Michalek007/ESC/ESC Pilot/Pomiary/test2_oscylacje.csv

Time |  |  | Oscillation (%) (avg) | Oscillation (%) (ref)
1749585122.7847323 | 45818.82781 | 0 | 900 | 3
1749585124.4796014 | 45818.82783 | 1.694869855 | 920.75 | 43.61
1749585125.9988434 | 45818.82785 | 3.214110131 | 663.98 | 79.34
1749585127.981447 | 45818.82787 | 5.196709768 | 509.51 | 84.6
1749585129.6124997 | 45818.82789 | 6.827759813 | 350.29 | 78.73
1749585131.2120302 | 45818.82791 | 8.427299769 | 268.96 | 74.82
1749585132.6668863 | 45818.82792 | 9.882150055 | 257.18 | 71.93
1749585134.2183836 | 45818.82794 | 11.43364976 | 210.25 | 67.7
1749585135.769585 | 45818.82796 | 12.98485023 | 179.14 | 64.11
1749585137.2725961 | 45818.82798 | 14.48785958 | 185.46 | 63.46
1749585138.7280366 | 45818.82799 | 15.94329954 | 168.78 | 63.39
1749585140.230938 | 45818.82801 | 17.44620013 | 149.09 | 60.42
1749585141.6537375 | 45818.82803 | 18.8689997 | 133.87 | 57.78
1749585143.0447867 | 45818.82804 | 20.26004966 | 141.51 | 57.1
1749585144.4378734 | 45818.82806 | 21.65313957 | 135.5 | 58.1
1749585145.8917708 | 45818.82808 | 23.10703935 | 123.63 | 55.82
1749585147.2827814 | 45818.82809 | 24.49804971 | 114.04 | 53.8
1749585148.8178267 | 45818.82811 | 26.03308966 | 106.03 | 51.97
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
