Michalek007/ESC/ESC Pilot/Pomiary/test3.csv

Time |  | Time | DutyCycle | ReferenceSpeed | AverageSpeed | MotorState | ró?nica
1749585731.840147 | 45818.83486 | 0 | 105 | 6000 | 6024 | RUN | 24 | Warto?? ?rednia zmierzona | 5999.493976
1749585732.942915 | 45818.83487 | 1.10277012 | 104 | 6000 | 6024 | RUN | 24 | Odchylenie od warto?ci zadanej | 0.506024096
1749585734.0938084 | 45818.83489 | 2.253660327 | 102 | 6000 | 5940 | RUN | -60 | Odchylenie od warto?ci zadanej [%] | 0.008434446
1749585735 | 45818.8349 | 3.389160102 | 105 | 6000 | 6084 | RUN | 84 | maksymalna odchy?ka | 270
1749585736.3650918 | 45818.83491 | 4.524949682 | 103 | 6000 | 5976 | RUN | -24 | odchylenie standardowe | 115.2588886
1749585737.5006552 | 45818.83492 | 5.660509807 | 102 | 6000 | 5928 | RUN | -72 | odchylenie standardowe [%] | 1.920981477
1749585868 | 45818.83643 | 136.1424697 | 105 | 6000 | 5964 | RUN | -36
1749585869 | 45818.83645 | 137.1655694 | 110 | 6000 | 6270 | RUN | 270
1749585870 | 45818.83646 | 0 | 107 | 6000 | 6162 | RUN | 162
1749585871 | 45818.83647 | 1.054739929 | 106 | 6000 | 6090 | RUN | 90
1749585872 | 45818.83649 | 2.093930379 | 102 | 6000 | 5934 | RUN | -66
1749585873 | 45818.8365 | 3.134009731 | 100 | 6000 | 5832 | RUN | -168
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
