Michalek007/ESC/ESC Pilot/Pomiary/test4.csv

Time | DutyCycle | ReferenceSpeed | AverageSpeed | MotorState
1749585855.6062152 | 801 | 4500 | 0 | IDLE
1749585857.748773 | 801 | 4500 | 0 | IDLE
1749585858.7722487 | 801 | 4500 | 0 | IDLE
1749585859.7950497 | 801 | 4500 | 0 | IDLE
1749585860.802953 | 801 | 4500 | 0 | IDLE
1749585861.7937887 | 801 | 4500 | 0 | IDLE
1749585862.8499117 | 801 | 4500 | 0 | IDLE
1749585863.9212673 | 233 | 4500 | 492 | START
1749585864.9446652 | 108 | 6000 | 3216 | RUN
1749585865.9522288 | 105 | 6000 | 5190 | RUN
1749585866.975492 | 102 | 6000 | 5664 | RUN
1749585867.9826145 | 105 | 6000 | 5964 | RUN
1749585869.00571 | 110 | 6000 | 6270 | RUN
1749585870.2697713 | 107 | 6000 | 6162 | RUN
1749585871.3245144 | 106 | 6000 | 6090 | RUN
1749585872.3637047 | 102 | 6000 | 5934 | RUN
1749585873.4037893 | 100 | 6000 | 5832 | RUN
1749585874.4749014 | 102 | 6000 | 5922 | RUN
1749585875.514549 | 100 | 6000 | 5862 | RUN
1749585876.5856402 | 102 | 6000 | 5934 | RUN
1749585877.5934482 | 104 | 6000 | 6006 | RUN
1749585878.5848978 | 105 | 6000 | 6054 | RUN
1749585879.5759685 | 104 | 6000 | 6036 | RUN
1749585880.583357 | 106 | 6000 | 6096 | RUN
1749585881.5907507 | 107 | 6000 | 6150 | RUN
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
